oliveres/3D/mega-fuse/images/01_assembly.png

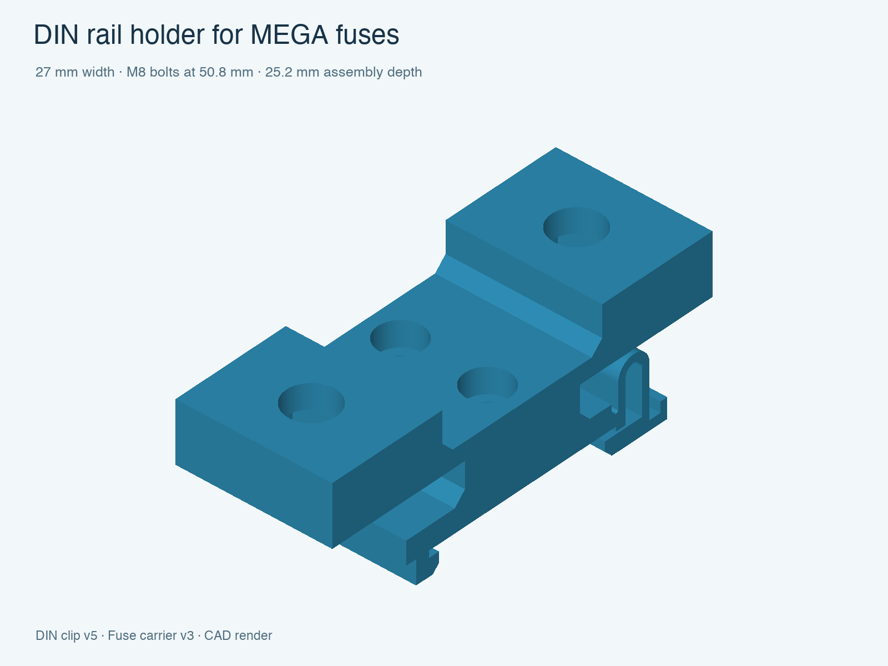
mega-fuse/images/01_assembly.png
